wntrblm/Hubble/firmware/motherboard/src/hubble.h

/*
    Copyright (c) 2021 Alethea Katherine Flowers.
    Published under the standard MIT License.
    Full text available at: https://opensource.org/licenses/MIT
*/

#pragma once

#include "hubble_ad5685.h"
#include "hubble_adc.h"
#include "hubble_calibration_table.h"
#include "hubble_calibration_table_load_save.h"
#include "hubble_config.h"
#include "hubble_dac.h"
#include "hubble_dotstar.h"
#include "hubble_math_utils.h"
#include "wntr_debug.h"
#include "wntr_midi.h"
#include "wntr_sercom_spi.h"
#include "wntr_usb.h"
