wntrblm/Hubble/firmware/src/drivers/stel_dotstar.c

/*
    Copyright (c) 2021 Alethea Katherine Flowers.
    Published under the standard MIT License.
    Full text available at: https://opensource.org/licenses/MIT
*/

#include "stel_dotstar.h"
#include "wntr_bitbang_spi.h"

#define DOTSTART_COUNT 1

static uint16_t brightness_ = 0;
static uint8_t pixels_[DOTSTART_COUNT * 3];
static const uint8_t start_frame_[4] = {0x00, 0x00, 0x00, 0x00};

/* Use bitband SPI for the dotstar since it's not connected to a real SERCOM. */
static struct WntrBitBangSPI spi_ = {
    .sdo = WNTR_GPIO_PIN(WNTR_PORT_A, 22),
    .sck = WNTR_GPIO_PIN(WNTR_PORT_A, 23),
    .clock_polarity = 0,
    .clock_phase = 0,
};

void stel_dotstar_init(uint8_t brightness) {
    brightness_ = brightness;
    wntr_bitbang_spi_init(&spi_, 48000000);
}

void stel_dotstar_set(size_t n, uint8_t r, uint8_t g, uint8_t b) {
    pixels_[n * 3] = (r * brightness_) >> 8;
    pixels_[n * 3 + 1] = (g * brightness_) >> 8;
    pixels_[n * 3 + 2] = (b * brightness_) >> 8;
}

void stel_dotstar_set32(size_t n, uint32_t color) {
    stel_dotstar_set(n, color >> 16 & 0xFF, color >> 8 & 0xFF, color & 0xFF);
}

void stel_dotstar_update() {
    wntr_bitbang_spi_write(&spi_, start_frame_, 4);
    for (size_t i = 0; i < DOTSTART_COUNT; i++) {
        wntr_bitbang_spi_write(&spi_, (uint8_t[]){0xFF}, 1);
        wntr_bitbang_spi_write(&spi_, pixels_ + (i * 3), 3);
    }
    for (size_t i = 0; i < DOTSTART_COUNT / 2 + 1; i++) { wntr_bitbang_spi_write(&spi_, (uint8_t[]){0x00}, 1); }
}
